InputBlackBoxOutput/Keystroker/pro micro/images/img 1.jpg

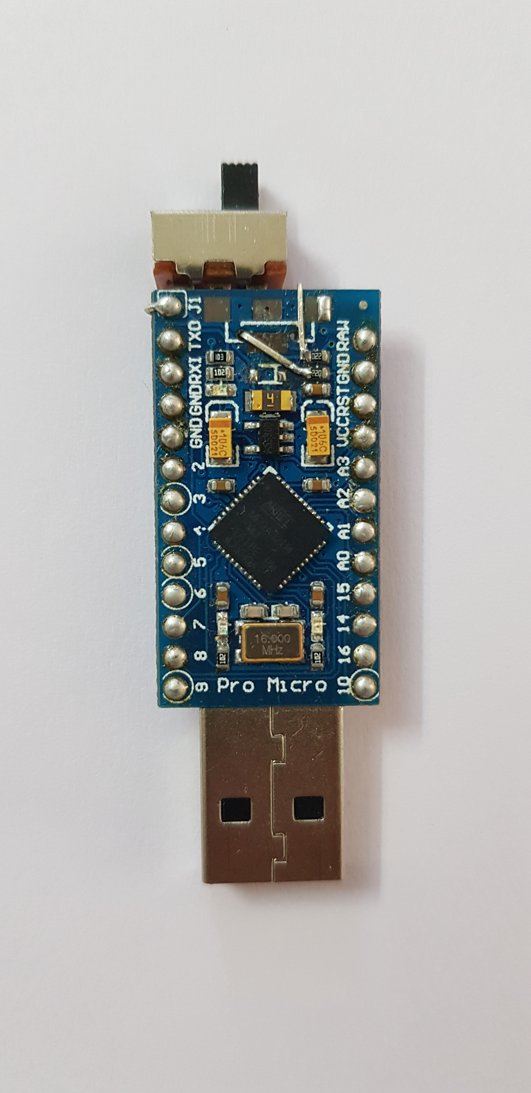
pro micro/images/img 1.jpg
