InputBlackBoxOutput/Keystroker/pro micro/images/img 2.jpg

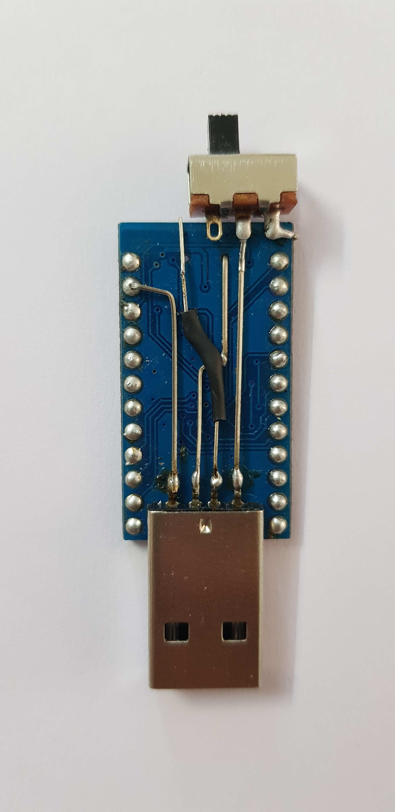
pro micro/images/img 2.jpg
