InputBlackBoxOutput/Keystroker/pro micro/images/img 3.jpg

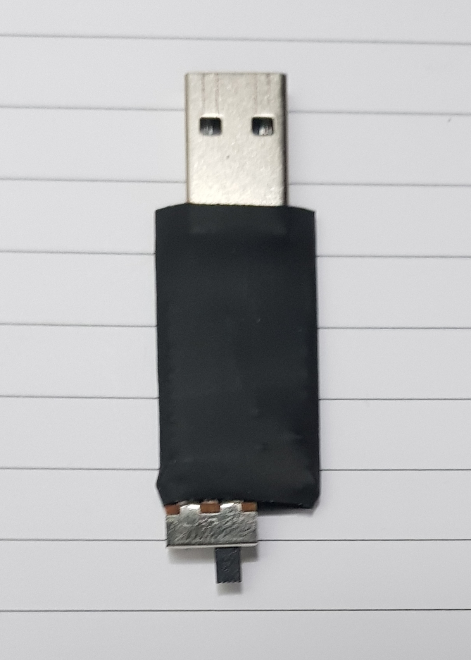
pro micro/images/img 3.jpg
