InputBlackBoxOutput/Keystroker/firmware/Guy Fawkes mask/keyboard.asm

_keyboardInit:

;keyboard.c,12 :: 		void keyboardInit() {
;keyboard.c,13 :: 		HID_Enable(readbuff, writebuff);
	MOVLW       _readbuff+0
	MOVWF       FARG_HID_Enable_readbuff+0 
	MOVLW       hi_addr(_readbuff+0)
	MOVWF       FARG_HID_Enable_readbuff+1 
	MOVLW       _writebuff+0
	MOVWF       FARG_HID_Enable_writebuff+0 
	MOVLW       hi_addr(_writebuff+0)
	MOVWF       FARG_HID_Enable_writebuff+1 
	CALL        _HID_Enable+0, 0
;keyboard.c,14 :: 		Delay_ms(1000);
	MOVLW       61
	MOVWF       R11, 0
	MOVLW       225
	MOVWF       R12, 0
	MOVLW       63
	MOVWF       R13, 0
L_keyboardInit0:
	DECFSZ      R13, 1, 1
	BRA         L_keyboardInit0
	DECFSZ      R12, 1, 1
	BRA         L_keyboardInit0
	DECFSZ      R11, 1, 1
	BRA         L_keyboardInit0
	NOP
	NOP
;keyboard.c,15 :: 		}
L_end_keyboardInit:
	RETURN      0
; end of _keyboardInit

_sendText:

;keyboard.c,17 :: 		void sendText(char* text) {
;keyboard.c,18 :: 		while( *text ) {
L_sendText1:
	MOVFF       FARG_sendText_text+0, FSR0
	MOVFF       FARG_sendText_text+1, FSR0H
	MOVF        POSTINC0+0, 1 
	BTFSC       STATUS+0, 2 
	GOTO        L_sendText2
;keyboard.c,19 :: 		sendKey(*text);
	MOVFF       FARG_sendText_text+0, FSR0
	MOVFF       FARG_sendText_text+1, FSR0H
	MOVF        POSTINC0+0, 0 
	MOVWF       FARG_sendKey+0 
	CALL        _sendKey+0, 0
;keyboard.c,20 :: 		text++;
	INFSNZ      FARG_sendText_text+0, 1 
	INCF        FARG_sendText_text+1, 1 
;keyboard.c,21 :: 		}
	GOTO        L_sendText1
L_sendText2:
;keyboard.c,22 :: 		}
L_end_sendText:
	RETURN      0
; end of _sendText

_sendKey:

;keyboard.c,35 :: 		void sendKey(char value) {
;keyboard.c,37 :: 		uint8_t type = 0x00;
	CLRF        sendKey_type_L0+0 
	CLRF        sendKey_modifier_L0+0 
;keyboard.c,40 :: 		if ( iscntrl(value) )
	MOVF        FARG_sendKey_value+0, 0 
	MOVWF       FARG_iscntrl_character+0 
	CALL        _iscntrl+0, 0
	MOVF        R0, 1 
	BTFSC       STATUS+0, 2 
	GOTO        L_sendKey3
;keyboard.c,41 :: 		type = 0x01;
	MOVLW       1
	MOVWF       sendKey_type_L0+0 
	GOTO        L_sendKey4
L_sendKey3:
;keyboard.c,43 :: 		else if ( isalpha(value) ) {
	MOVF        FARG_sendKey_value+0, 0 
	MOVWF       FARG_isalpha_character+0 
	CALL        _isalpha+0, 0
	MOVF        R0, 1 
	BTFSC       STATUS+0, 2 
	GOTO        L_sendKey5
;keyboard.c,44 :: 		type = 0x02;
	MOVLW       2
	MOVWF       sendKey_type_L0+0 
;keyboard.c,45 :: 		if ( isupper(value) )
	MOVF        FARG_sendKey_value+0, 0 
	MOVWF       FARG_isupper_character+0 
	CALL        _isupper+0, 0
	MOVF        R0, 1 
	BTFSC       STATUS+0, 2 
	GOTO        L_sendKey6
;keyboard.c,46 :: 		modifier = KEY_MOD_LSHIFT;
	MOVLW       2
	MOVWF       sendKey_modifier_L0+0 
	GOTO        L_sendKey7
L_sendKey6:
;keyboard.c,48 :: 		modifier = 0x00;
	CLRF        sendKey_modifier_L0+0 
L_sendKey7:
;keyboard.c,49 :: 		}
	GOTO        L_sendKey8
L_sendKey5:
;keyboard.c,51 :: 		else if ( isdigit(value) )
	MOVF        FARG_sendKey_value+0, 0 
	MOVWF       FARG_isdigit_character+0 
	CALL        _isdigit+0, 0
	MOVF        R0, 1 
	BTFSC       STATUS+0, 2 
	GOTO        L_sendKey9
;keyboard.c,52 :: 		type = 0x03;
	MOVLW       3
	MOVWF       sendKey_type_L0+0 
	GOTO        L_sendKey10
L_sendKey9:
;keyboard.c,54 :: 		type = 0x04;
	MOVLW       4
	MOVWF       sendKey_type_L0+0 
L_sendKey10:
L_sendKey8:
L_sendKey4:
;keyboard.c,57 :: 		switch(type) {
	GOTO        L_sendKey11
;keyboard.c,58 :: 		case 0x01:
L_sendKey13:
;keyboard.c,59 :: 		if( value == '\r' || value == '\n' )  value = KEY_ENTER;
	MOVF        FARG_sendKey_value+0, 0 
	XORLW       13
	BTFSC       STATUS+0, 2 
	GOTO        L__sendKey122
	MOVF        FARG_sendKey_value+0, 0 
	XORLW       10
	BTFSC       STATUS+0, 2 
	GOTO        L__sendKey122
	GOTO        L_sendKey16
L__sendKey122:
	MOVLW       40
	MOVWF       FARG_sendKey_value+0 
	GOTO        L_sendKey17
L_sendKey16:
;keyboard.c,60 :: 		else if( value == '\t' )              value = KEY_TAB;
	MOVF        FARG_sendKey_value+0, 0 
	XORLW       9
	BTFSS       STATUS+0, 2 
	GOTO        L_sendKey18
	MOVLW       43
	MOVWF       FARG_sendKey_value+0 
	GOTO        L_sendKey19
L_sendKey18:
;keyboard.c,61 :: 		else if( value == '\b' )              value = KEY_BACKSPACE;
	MOVF        FARG_sendKey_value+0, 0 
	XORLW       8
	BTFSS       STATUS+0, 2 
	GOTO        L_sendKey20
	MOVLW       42
	MOVWF       FARG_sendKey_value+0 
L_sendKey20:
L_sendKey19:
L_sendKey17:
;keyboard.c,62 :: 		break;
	GOTO        L_sendKey12
;keyboard.c,64 :: 		case 0x02:
L_sendKey21:
;keyboard.c,66 :: 		value = toupper(value);
	MOVF        FARG_sendKey_value+0, 0 
	MOVWF       FARG_toupper_character+0 
	CALL        _toupper+0, 0
	MOVF        R0, 0 
	MOVWF       FARG_sendKey_value+0 
;keyboard.c,69 :: 		value = value - 'A' + KEY_A;
	MOVLW       65
	SUBWF       R0, 0 
	MOVWF       FARG_sendKey_value+0 
	MOVLW       4
	ADDWF       FARG_sendKey_value+0, 1 
;keyboard.c,70 :: 		break;
	GOTO        L_sendKey12
;keyboard.c,72 :: 		case 0x03:
L_sendKey22:
;keyboard.c,73 :: 		if ( value == '0' )
	MOVF        FARG_sendKey_value+0, 0 
	XORLW       48
	BTFSS       STATUS+0, 2 
	GOTO        L_sendKey23
;keyboard.c,74 :: 		value = KEY_KP0;
	MOVLW       98
	MOVWF       FARG_sendKey_value+0 
	GOTO        L_sendKey24
L_sendKey23:
;keyboard.c,76 :: 		value = value - '1' + KEY_KP1;
	MOVLW       49
	SUBWF       FARG_sendKey_value+0, 1 
	MOVLW       89
	ADDWF       FARG_sendKey_value+0, 1 
L_sendKey24:
;keyboard.c,77 :: 		break;
	GOTO        L_sendKey12
;keyboard.c,79 :: 		case 0x04:
L_sendKey25:
;keyboard.c,80 :: 		if ( value == '-' || value == '_') {
	MOVF        FARG_sendKey_value+0, 0 
	XORLW       45
	BTFSC       STATUS+0, 2 
	GOTO        L__sendKey121
	MOVF        FARG_sendKey_value+0, 0 
	XORLW       95
	BTFSC       STATUS+0, 2 
	GOTO        L__sendKey121
	GOTO        L_sendKey28
L__sendKey121:
;keyboard.c,81 :: 		if( value == '_') modifier = KEY_MOD_LSHIFT;
	MOVF        FARG_sendKey_value+0, 0 
	XORLW       95
	BTFSS       STATUS+0, 2 
	GOTO        L_sendKey29
	MOVLW       2
	MOVWF       sendKey_modifier_L0+0 
L_sendKey29:
;keyboard.c,82 :: 		value = KEY_MINUS;
	MOVLW       45
	MOVWF       FARG_sendKey_value+0 
;keyboard.c,83 :: 		}
	GOTO        L_sendKey30
L_sendKey28:
;keyboard.c,85 :: 		else if ( value == '+' || value == '=' ) {
	MOVF        FARG_sendKey_value+0, 0 
	XORLW       43
	BTFSC       STATUS+0, 2 
	GOTO        L__sendKey120
	MOVF        FARG_sendKey_value+0, 0 
	XORLW       61
	BTFSC       STATUS+0, 2 
	GOTO        L__sendKey120
	GOTO        L_sendKey33
L__sendKey120:
;keyboard.c,86 :: 		if( value == '=' ) modifier = KEY_MOD_LSHIFT;
	MOVF        FARG_sendKey_value+0, 0 
	XORLW       61
	BTFSS       STATUS+0, 2 
	GOTO        L_sendKey34
	MOVLW       2
	MOVWF       sendKey_modifier_L0+0 
L_sendKey34:
;keyboard.c,87 :: 		value = KEY_EQUAL;
	MOVLW       46
	MOVWF       FARG_sendKey_value+0 
;keyboard.c,88 :: 		}
	GOTO        L_sendKey35
L_sendKey33:
;keyboard.c,90 :: 		else if ( value == '{' || value == '[' ) {
	MOVF        FARG_sendKey_value+0, 0 
	XORLW       123
	BTFSC       STATUS+0, 2 
	GOTO        L__sendKey119
	MOVF        FARG_sendKey_value+0, 0 
	XORLW       91
	BTFSC       STATUS+0, 2 
	GOTO        L__sendKey119
	GOTO        L_sendKey38
L__sendKey119:
;keyboard.c,91 :: 		if ( value == '{' ) modifier = KEY_MOD_LSHIFT;
	MOVF        FARG_sendKey_value+0, 0 
	XORLW       123
	BTFSS       STATUS+0, 2 
	GOTO        L_sendKey39
	MOVLW       2
	MOVWF       sendKey_modifier_L0+0 
L_sendKey39:
;keyboard.c,92 :: 		value = KEY_LEFTBRACE;
	MOVLW       47
	MOVWF       FARG_sendKey_value+0 
;keyboard.c,93 :: 		}
	GOTO        L_sendKey40
L_sendKey38:
;keyboard.c,95 :: 		else if ( value == '}' || value == ']' ) {
	MOVF        FARG_sendKey_value+0, 0 
	XORLW       125
	BTFSC       STATUS+0, 2 
	GOTO        L__sendKey118
	MOVF        FARG_sendKey_value+0, 0 
	XORLW       93
	BTFSC       STATUS+0, 2 
	GOTO        L__sendKey118
	GOTO        L_sendKey43
L__sendKey118:
;keyboard.c,96 :: 		if ( value == '}' ) modifier = KEY_MOD_LSHIFT;
	MOVF        FARG_sendKey_value+0, 0 
	XORLW       125
	BTFSS       STATUS+0, 2 
	GOTO        L_sendKey44
	MOVLW       2
	MOVWF       sendKey_modifier_L0+0 
L_sendKey44:
;keyboard.c,97 :: 		value = KEY_RIGHTBRACE;
	MOVLW       48
	MOVWF       FARG_sendKey_value+0 
;keyboard.c,98 :: 		}
	GOTO        L_sendKey45
L_sendKey43:
;keyboard.c,100 :: 		else if ( value == '\\' || value == '|' ) {
	MOVF        FARG_sendKey_value+0, 0 
	XORLW       92
	BTFSC       STATUS+0, 2 
	GOTO        L__sendKey117
	MOVF        FARG_sendKey_value+0, 0 
	XORLW       124
	BTFSC       STATUS+0, 2 
	GOTO        L__sendKey117
	GOTO        L_sendKey48
L__sendKey117:
;keyboard.c,101 :: 		if( value == '|' ) modifier = KEY_MOD_LSHIFT;
	MOVF        FARG_sendKey_value+0, 0 
	XORLW       124
	BTFSS       STATUS+0, 2 
	GOTO        L_sendKey49
	MOVLW       2
	MOVWF       sendKey_modifier_L0+0 
L_sendKey49:
;keyboard.c,102 :: 		value = KEY_BACKSLASH;
	MOVLW       49
	MOVWF       FARG_sendKey_value+0 
;keyboard.c,103 :: 		}
	GOTO        L_sendKey50
L_sendKey48:
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
	CLRF        1349 
;keyboard.c,205 :: 		writebuff[6] = 0x00;
	CLRF        1350 
;keyboard.c,206 :: 		writebuff[7] = 0x00;
	CLRF        1351 
;keyboard.c,207 :: 		while( !HID_Write(writebuff,8) );
L_sendKey105:
	MOVLW       _writebuff+0
	MOVWF       FARG_HID_Write_writebuff+0 
	MOVLW       hi_addr(_writebuff+0)
	MOVWF       FARG_HID_Write_writebuff+1 
	MOVLW       8
	MOVWF       FARG_HID_Write_len+0 
	CALL        _HID_Write+0, 0
	MOVF        R0, 1 
	BTFSS       STATUS+0, 2 
	GOTO        L_sendKey106
	GOTO        L_sendKey105
L_sendKey106:
;keyboard.c,208 :: 		Delay_ms(30);
	MOVLW       2
	MOVWF       R11, 0
	MOVLW       212
	MOVWF       R12, 0
	MOVLW       133
	MOVWF       R13, 0
L_sendKey107:
	DECFSZ      R13, 1, 1
	BRA         L_sendKey107
	DECFSZ      R12, 1, 1
	BRA         L_sendKey107
	DECFSZ      R11, 1, 1
	BRA         L_sendKey107
;keyboard.c,211 :: 		writebuff[0] = 0x00;  // Modifier
	CLRF        1344 
;keyboard.c,212 :: 		writebuff[2] = 0x00;
	CLRF        1346 
;keyboard.c,213 :: 		while( !HID_Write(writebuff,8) );
L_sendKey108:
	MOVLW       _writebuff+0
	MOVWF       FARG_HID_Write_writebuff+0 
	MOVLW       hi_addr(_writebuff+0)
	MOVWF       FARG_HID_Write_writebuff+1 
	MOVLW       8
	MOVWF       FARG_HID_Write_len+0 
	CALL        _HID_Write+0, 0
	MOVF        R0, 1 
	BTFSS       STATUS+0, 2 
	GOTO        L_sendKey109
	GOTO        L_sendKey108
L_sendKey109:
;keyboard.c,214 :: 		Delay_ms(30);
	MOVLW       2
	MOVWF       R11, 0
	MOVLW       212
	MOVWF       R12, 0
	MOVLW       133
	MOVWF       R13, 0
L_sendKey110:
	DECFSZ      R13, 1, 1
	BRA         L_sendKey110
	DECFSZ      R12, 1, 1
	BRA         L_sendKey110
	DECFSZ      R11, 1, 1
	BRA         L_sendKey110
;keyboard.c,215 :: 		}
L_end_sendKey:
	RETURN      0
; end of _sendKey
